sparkfun/SparkFun_Thing_Plus_RP2350/docs/assets/img/Thing-Plus-RP2350-Camera-Demo-2.jpg

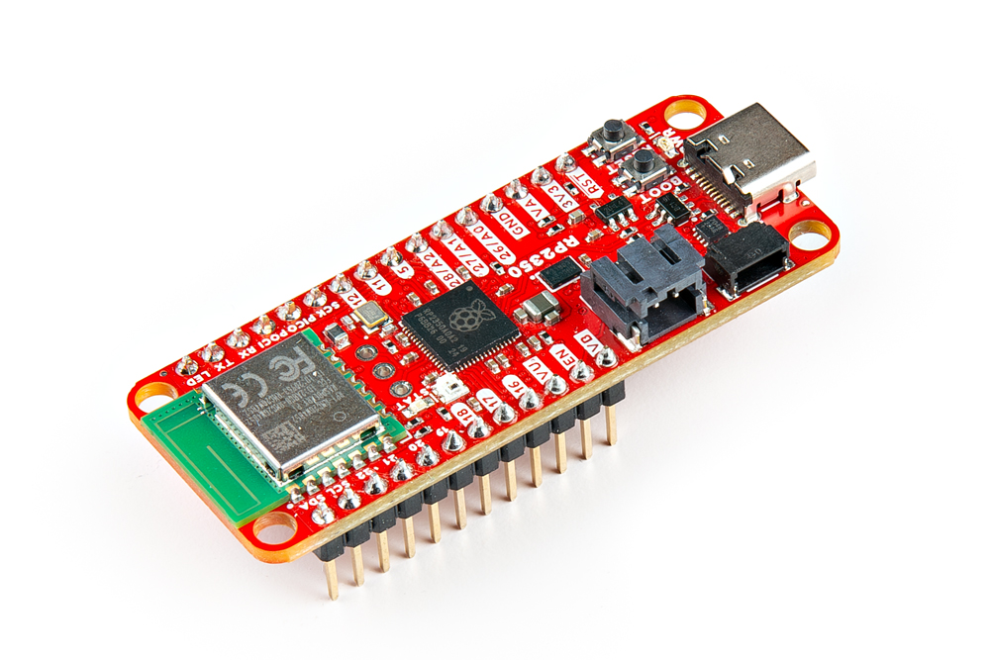
docs/assets/img/Thing-Plus-RP2350-Camera-Demo-2.jpg
